spencelab/triggerbox_ros2/triggerbox_ros2/triggerbox_device.py

#!/usr/bin/env python3
import serial
import numpy as np
import os, sys, time, threading, queue, collections
import struct
import argparse
import logging

from triggerbox_ros2.time_model import get_time_model, TimeFitError
# By default we require arduino_udev_ros2 to be install! download that 
# repo and use ./install.sh in it's root dir to put this arduinoudev 
# library on the system. that is better.
# If you really want to run the system without doing that, uncomment
# the line below and comment out the one after. it will use a local
# version of the library but it may be out of date!
#from triggerbox_ros2.arduinoudev import serial_handshake
from arduinoudev import serial_handshake

def uint32(b0,b1,b2,b3):
    return (b3 << 24) + (b2 << 16) + (b1 << 8) + b0

def uint16(b0,b1):
    return (b1 << 8) + b0

if sys.platform.startswith('win'):
    time_func = time.clock
else:
    time_func = time.time

QUERY_DT = 1.0 # n seconds between clock info requests

# Measured on 6 September 2013
LOW_VOLTS = 0.0063
HIGH_VOLTS = 4.13
RANGE_VOLTS = HIGH_VOLTS-LOW_VOLTS

class SerialThread(threading.Thread):
    def __init__(self,args,device):
        super(SerialThread,self).__init__(name="triggerbox serial thread",)
        self.__args=args
        self._aout_seq = 0
        self.ICR1_AND_PRESCALER = None

        self.device = device

        self.version_check_done = False
        self.firmware_version = None
        self.output_enabled = False

        self._last_aout_sequence = None, None, None
        self._log = logging.getLogger("root.serial")

    def _set_ICR1_AND_PRESCALER( self, new_value ):
        icr1, prescaler = new_value
        #print(icr1)
        #print(prescaler)
        #50000 -> this is for 5Hz...
        #64
        # https://docs.python.org/3/library/struct.html
        # 
        chars = struct.pack('<H',icr1) # little-endian unsigned short
        #print(chars)
        #print(type(chars))
        #b'P\xc3'
        #<class 'bytes'>
        # Equation for frequency: (for 250Hz) - see code below, ignores the 1.
        # f_pwm=f_clock/(N*(1+TOP))
        # choose scaler=64.
        # f_pwm=16e6/(64*(1+TOP))
        # 64*(1+TOP)=16e6/f_pwm
        # TOP=16e6/(f_pwm*64) - 1=999
        assert len(chars)==2
        #vals = [ord(c) for c in chars] <- this makes a list of ints? https://www.w3schools.com/python/ref_func_ord.asp
        vals = chars # in python3 chars as bytes can be shift operated with <<
        # confirmed that operation below for python3 reproduces eg icr1 50000 when that is input.
        self.ICR1_AND_PRESCALER = ((vals[1] << 8) + vals[0], prescaler)
        assert self.ICR1_AND_PRESCALER==new_value
        # Ok - this was just going to append the character 1 or 2 
        # to the output string. The firmware just uses 1 and 2 as
        # keys to set either 8 or 64...
        if prescaler==8:
            chars += b'1'
        elif prescaler==64:
            chars += b'2'
        else:
            raise ValueError('unsupported prescaler: %s'%prescaler)
        self.ser.write(b'T='+chars)

    def _set_AOUT( self, aout0, aout1 ):
        aout0_chars = struct.pack('<H', aout0) # little-endian unsigned short
        assert len(aout0_chars)==2
        aout1_chars = struct.pack('<H', aout1) # little-endian unsigned short
        assert len(aout1_chars)==2
        chars = aout0_chars + aout1_chars + chr(self._aout_seq)
        self.ser.write(b'O='+chars)
        self._last_aout_sequence = self._aout_seq, aout0, aout1
        self._aout_seq += 1
        self._aout_seq = self._aout_seq % 256

    def run(self):
        name = serial_handshake(self.device)
        self._log.info('connected to device named %r' % name)

        self._qi = 0
        self._queries = collections.OrderedDict()

        now = time_func()

        self._version_check_started = False
        self._connect_time = now
        self._vquery_time = now + 1.0   #wait 1 second before first version query
        self._last_time = self._vquery_time + 1.0   #and 1 second after version query

        self.raw_q, self.time_q, self.outq, self.aout_q = self.__args

        self.ser = serial.Serial(port=self.device,
                                 timeout=0.01,
                                 baudrate=115200)

        buf = b''
        while 1:

            # handle new commands
            while 1:
                try:
                    cmd_tup = self.outq.get_nowait()
                    cmd = cmd_tup[0]
                    if cmd=='icr1_and_prescaler':
                        new_value = cmd_tup[1]
                        self._set_ICR1_AND_PRESCALER( new_value )
                    elif cmd=='stop_pulses_and_reset':
                        self.ser.write('S0'.encode('utf-8'))
                    elif cmd=='start_pulses':
                        self.ser.write('S1'.encode('utf-8'))
                    elif cmd=='stop_pulses':
                        self.ser.write('S2'.encode('utf-8'))
                    elif cmd=='set_output_enabled':
                        enabled = bool(cmd_tup[1])
                        self.ser.write(('E1' if enabled else 'E0').encode('utf-8'))
                        self.output_enabled = enabled
                    elif cmd=='AOut':
                        aout0, aout1 = cmd_tup[1:3]
                        self._set_AOUT( aout0, aout1 )
                except queue.Empty:
                    break

            # get all pending data
            buf += self.ser.read()

            # handle pending data
            buf = self._h(buf)

            now = time_func()

            # perform any ongoing tasks
            if self.version_check_done:
                # request sample
                if (now - self._last_time) > QUERY_DT:
                    self._queries[ self._qi ] = now
                    tosend = b'P' + self._qi.to_bytes(1,'little')
                    #self._log.debug("Sending query %d" % self._qi)
                    #self._log.debug"Sending over serial %s" % tosend )
                    self.ser.write( tosend )
                    self._qi = (self._qi + 1) % 256
                    self._last_time = now
            else:
                # request firmware version
                if not self._version_check_started:
                    if now >= self._vquery_time:
                        self._log.info('checking firmware version')
                        self.ser.write( b'V?' )
                        self._version_check_started = True
                        self._vquery_time = now
                #retry every second
                if (now - self._vquery_time) > 1.0:
                    self._version_check_started = False
                #give up after 20 seconds
                if (now - self._connect_time) > 20.0:
                    raise RuntimeError('no version response')

    def _handle_version(self, value, pulsenumber, count):
        # Firmware version 13 is the legacy ROS2 triggerbox protocol.
        # Version 14 adds E0/E1 output blanking while Timer1 keeps running.
        if value < 13:
            raise RuntimeError('unsupported triggerbox firmware version %d' % value)
        self._vquery_time = time_func()
        self.firmware_version = value
        self.version_check_done = value
        self._log.info('connected to triggerbox firmware version %d' % value )

    def _handle_returned_timestamp(self, qi, pulsenumber, count):
        now = time_func()

        while len(self._queries) > 50:
            old_qi = self._queries.popitem(last=False)
            self._log.warn('never got return for query %d'%old_qi)

        try:
            send_timestamp = self._queries.pop( qi )
        except KeyError:
            self._log.warn('could not find original data for query %d'%qi)
            return

        max_error = now-send_timestamp
        if max_error > 0.015: # 15 msec cutoff
            self._log.warn(
                'clock sample took %.1f msec. Ignoring value.'%( max_error*1e3))
            return

        ino_time_estimate = (now+send_timestamp)*0.5

        if self.ICR1_AND_PRESCALER is None:
            self._log.warning('No clock measurements until framerate set.')
            return

        icr1, prescaler = self.ICR1_AND_PRESCALER
        frac = float(count)/icr1
        ino_stamp = pulsenumber + frac

        self.time_q.put( (ino_time_estimate, ino_stamp) )

        self.raw_q.put( (send_timestamp, pulsenumber,
                         int(np.round(frac * 255.0)), now) )

    def _handle_returned_aout(self, seq, pulsenumber, count):
        orig_seq, aout0, aout1 = self._last_aout_sequence
        if seq != orig_seq:
            self._log.warn('AOUT confirmation has wrong sequence number.')
            return

        if self.ICR1_AND_PRESCALER is None:
            self._log.warn('No AOUT confirmation until framerate set.')
            return

        icr1, prescaler = self.ICR1_AND_PRESCALER
        frac = float(count)/icr1

        self.aout_q.put( (pulsenumber, int(np.round(frac * 255.0)),
                          aout0, aout1))

    def _h(self,buf):
        result = buf
        #print(type(buf))
        #print(buf)
        if len(buf) >= 3: # header, length, checksum is minimum
            valid = False

            packet_type = buf[0:1].decode('UTF8')
            payload_len = buf[1]

            #print(packet_type)
            #print(type(packet_type))
            min_valid_packet_size = 3+payload_len  # header (2) + payload + checksum (1)
            if len(buf) >= min_valid_packet_size:
                expected_chksum = buf[2+payload_len]

                check_buf = buf[2:-1]
                #bytes = [ord(char) for char in check_buf]
                #actual_chksum = sum( bytes ) % 256
                actual_chksum = sum( check_buf ) % 256

                if actual_chksum == expected_chksum:
                    valid = True
                    n_used_chars = len(check_buf)+3
                else:
                    raise RuntimeError('checksum mismatch')

                if packet_type in ('P','V','O'):
                    assert payload_len==7
                    value = check_buf[0]
                    e0,e1,e2,e3 = check_buf[1:5]
                    t0,t1 = check_buf[5:7]

                    pulsenumber = uint32(e0,e1,e2,e3)
                    count = uint16(t0,t1)
                    #print(value)
                    if packet_type == 'P':
                        self._handle_returned_timestamp(value, pulsenumber, count )
                    elif packet_type == 'V':
                        self._handle_version(value, pulsenumber, count )
                    elif packet_type == 'O':
                        self._handle_returned_aout(value, pulsenumber, count )
                else:
                    raise ValueError('unknown packet type')

            if valid:
                result = buf[n_used_chars:]

        return result

def volts_to_dac(volts):
    v = np.clip(volts,LOW_VOLTS,HIGH_VOLTS)
    v0 = v-LOW_VOLTS
    v0_frac = v0/RANGE_VOLTS
    dac_float = v0_frac*4095
    dac = int(np.round(dac_float))
    return dac

def queue_to_func(q,func):
    while 1:
        raw = q.get()
        func(*raw)

class TriggerboxDevice(threading.Thread):

    def __init__(self, device):
        # python3 below might just be super()
        super(TriggerboxDevice,self).__init__(name="triggerbox device")
        self.daemon = True

        self._connected = False
        self._log = logging.getLogger("trigger.device")
        logging.basicConfig(level=logging.DEBUG)
        self.raw_q = queue.Queue()
        self.time_q = queue.Queue()
        self.outq = queue.Queue()
        self.aout_q = queue.Queue()
        aout_sender_thread = threading.Thread( target=queue_to_func,
                                               args=(self.aout_q,
                                                     self._notify_aout_confirm),
                                               )
        aout_sender_thread.daemon = True
        aout_sender_thread.start()

        self.expected_trigger_rate = np.nan

        self.times = []

        self.ser_thread = SerialThread(args=(
            self.raw_q,self.time_q,self.outq,self.aout_q),
                                       device=device)
        self.ser_thread.daemon = True
        self.ser_thread.start()

        self._log.info('Waiting until serial device confirmed...')
        while True:
            if not self.ser_thread.is_alive():
                raise RuntimeError('serial thread died')
            if self.ser_thread.version_check_done:
                break
            time.sleep(0.1)

        self._connected = True
        self._notify_connected('v:%s' % self.ser_thread.version_check_done, device)

        #we need to talk to the serial device reguarly, so we implement
        #our own scheduler here
        self.start()

    def _clear_data(self):
        self.times = []
        self.time_model = None
        self._notify_clockmodel(np.nan, np.nan)

    def _trim_data(self,_=None):
        keep_n_times = 500

        if len(self.times) > keep_n_times:
            del self.times[-keep_n_times:]
        return True

    def _get_new_data(self, _=None):
        if not self.ser_thread.is_alive():
            self._notify_fatal_error('serial port thread is not alive')
            return

        # get all pending data
        while 1:
            try:
                raw = self.raw_q.get_nowait()
                self._notify_clock_measurement(*raw)
            except queue.Empty:
                break

        new_time = False
        while 1:
            try:
                self.times.append( self.time_q.get_nowait() )
                new_time = True
            except queue.Empty:
                break

        if new_time and len(self.times) > 3:
            # require 3 samples to start attempting to fit model
            tdata = np.array(self.times[-100:])
            try:
                self.time_model = get_time_model(tdata[:,1], tdata[:,0], max_residual=0.1)
            except TimeFitError as err:
                self._log.warn('error fitting time_model: %s'%err)
            else:
                self._notify_clockmodel(self.time_model.gain, self.time_model.offset)
                approx_freq = 1.0/self.time_model.gain
                self._log.debug('approximate timer frequency: %s'%(approx_freq,))

    def _notify_framerate(self, expected_trigger_rate):
        self._log.info('framerate: %f' % expected_trigger_rate)

    def _notify_clockmodel(self, gain, offset):
        self._log.info('gain: %s offset: %s' % (gain, offset))

    def _notify_clock_measurement(self, start_timestamp, pulsenumber, fraction_n_of_255, stop_timestamp):
        pass

    def _notify_aout_confirm(self, pulsenumber, fraction_n_of_255, aout0, aout1):
        pass

    def _notify_fatal_error(self, msg):
        self._log.critical(msg)

    def _notify_connected(self, name, device):
        self._log.info("connected to %s" % device)

    def run(self):
        i = 0
        while True:
            if (i % 100) == 0:
                self._get_new_data()
            if i == 2000:
                self._trim_data()
                i = 0
            i += 10
            time.sleep(0.01)

    def set_triggerrate(self, rate_ideal):

        if rate_ideal == 0:
            self._log.info('triggerbox_device: setting FPS to ZERO')
            self.outq.put( ('stop_pulses',) )
            self._clear_data()
            self.expected_trigger_rate = rate_ideal
            self._notify_framerate(self.expected_trigger_rate)
            return

        def get_rate(rate_ideal, prescaler):
            xtal = 16e6 # 16 MHz clock
            base_clock = xtal/float(prescaler)
            new_top_ideal = base_clock/rate_ideal
            new_icr1 = int(np.clip(np.round(new_top_ideal),0,0xFFFF))
            rate_actual = base_clock/new_icr1
            return new_icr1, rate_actual

        self._log.info('received set_triggerrate command with target of %s'%rate_ideal)
        self._clear_data()

        icr1_8, rate_actual_8 = get_rate( rate_ideal, 8)
        icr1_64, rate_actual_64 = get_rate( rate_ideal, 64)

        error_8  = abs(rate_ideal-rate_actual_8)
        error_64 = abs(rate_ideal-rate_actual_64)

        if error_8 < error_64:
            new_icr1 = icr1_8
            rate_actual = rate_actual_8
            prescaler = 8
        else:
            new_icr1 = icr1_64
            rate_actual = rate_actual_64
            prescaler = 64

        self._log.info( 'desired rate %s (actual rate %s) using ICR1_AND_PRESCALER 0x%X %d' % (rate_ideal,
                                                                                            rate_actual,
                                                                                            new_icr1,
                                                                                            prescaler) )
        self.expected_trigger_rate = np.nan
        self._notify_framerate(self.expected_trigger_rate)

        self.outq.put( ('stop_pulses_and_reset',) ) # stop clock, reset pulsecounter
        self.outq.put( ('icr1_and_prescaler', (new_icr1,prescaler)) ) # set triggerrate
        self._clear_data() # clear old data
        self.outq.put( ('start_pulses',) ) # stop clock, reset pulsecounter

        self.expected_trigger_rate = rate_actual
        self._notify_framerate(self.expected_trigger_rate)

    def pause_and_reset(self, pause_duration_seconds):
        orig_value = self.expected_trigger_rate
        self.expected_trigger_rate = np.nan
        self._notify_framerate(self.expected_trigger_rate)

        self.outq.put( ('stop_pulses_and_reset',) ) # stop clock, reset pulsecounter
        self._clear_data() # clear old data
        time.sleep(pause_duration_seconds)
        self._clear_data() # clear old data
        self.outq.put( ('start_pulses',) ) # stop clock, reset pulsecounter

        self.expected_trigger_rate = orig_value
        self._notify_framerate(self.expected_trigger_rate)

    def set_output_enabled(self, enabled):
        enabled = bool(enabled)
        self._log.info('triggerbox_device: setting trigger output enabled=%s' % enabled)
        self.outq.put( ('set_output_enabled', enabled) )

    def enable_output(self):
        self.set_output_enabled(True)

    def disable_output(self):
        self.set_output_enabled(False)

    def start_clock(self):
        self._log.info('triggerbox_device: starting trigger clock')
        self.outq.put( ('start_pulses',) )

    def stop_clock(self):
        self._log.info('triggerbox_device: stopping trigger clock')
        self.outq.put( ('stop_pulses',) )

    def set_aout_ab_volts(self, aout0_v, aout1_v):
        aout0 = volts_to_dac(aout0_v)
        aout1 = volts_to_dac(aout1_v)
        self.outq.put( ('AOut', aout0, aout1) ) # set AOUT

    def set_aout_ab_raw(self, aout0, aout1):
        self.outq.put( ('AOut', aout0, aout1) ) # set AOUT

if __name__=='__main__':
    import sys
    import itertools

    try:
        port = sys.argv[1]
    except IndexError:
        port = '/dev/ttyUSB0'

    logging.basicConfig(level=logging.DEBUG)
    td = TriggerboxDevice(port)
    for i in itertools.cycle(range(5,200,10)):
    #for i in itertools.cycle([125,250]):
        td.set_triggerrate(i)
        time.sleep(10)
